MaulikItaliya/Custom-Arduino-Compatible-Board-Design-Altium-/arduino-pcb-design/hardware/Footprint 3d/1825910-6--3DModel-STEP-418109.STEP

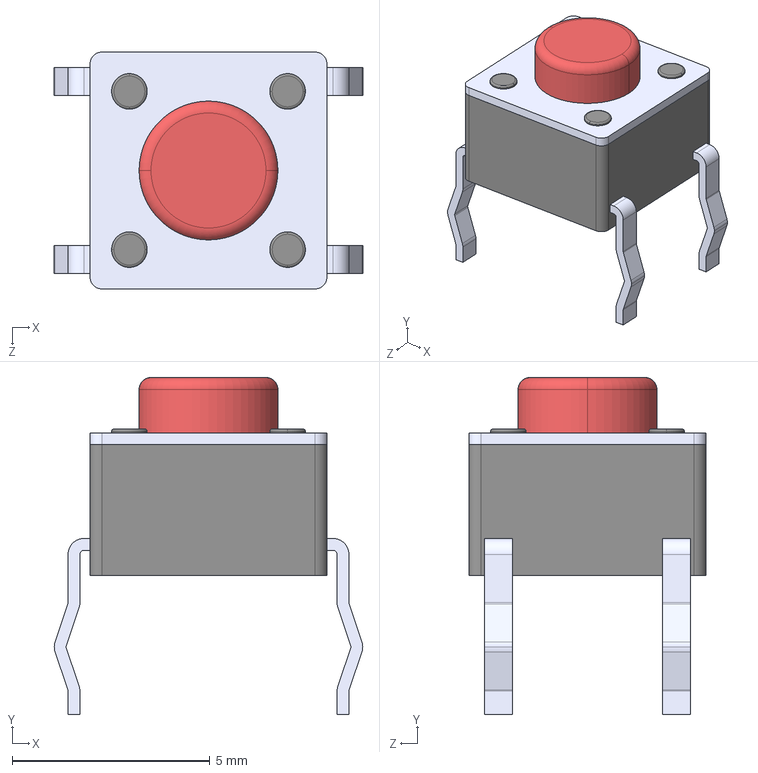
[picture p19: CAD file, 2026-05-17]
arduino-pcb-design/hardware/Footprint 3d/1825910-6--3DModel-STEP-418109.STEP
7.80 x 8.52 x 5.99 mm
