MaulikItaliya/Custom-Arduino-Compatible-Board-Design-Altium-/arduino-pcb-design/hardware/Footprint 3d/m20-7820842.stp

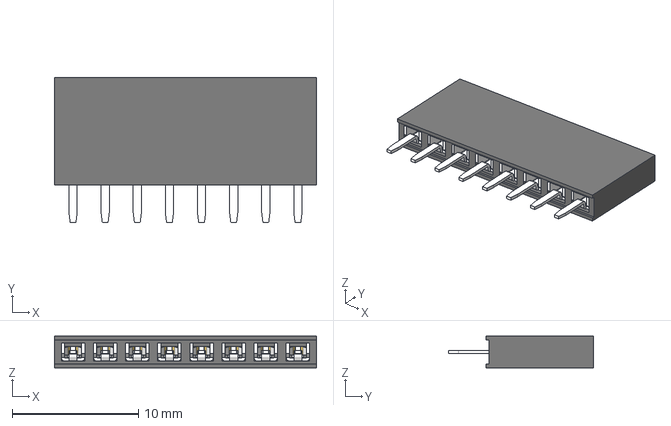
[picture p20: CAD file, 2026-05-17]
arduino-pcb-design/hardware/Footprint 3d/m20-7820842.stp
20.7 x 11.5 x 2.50 mm
