MaulikItaliya/Custom-Arduino-Compatible-Board-Design-Altium-/arduino-pcb-design/hardware/Footprint 3d/68000-103HLF--3DModel-STEP-533217.STEP

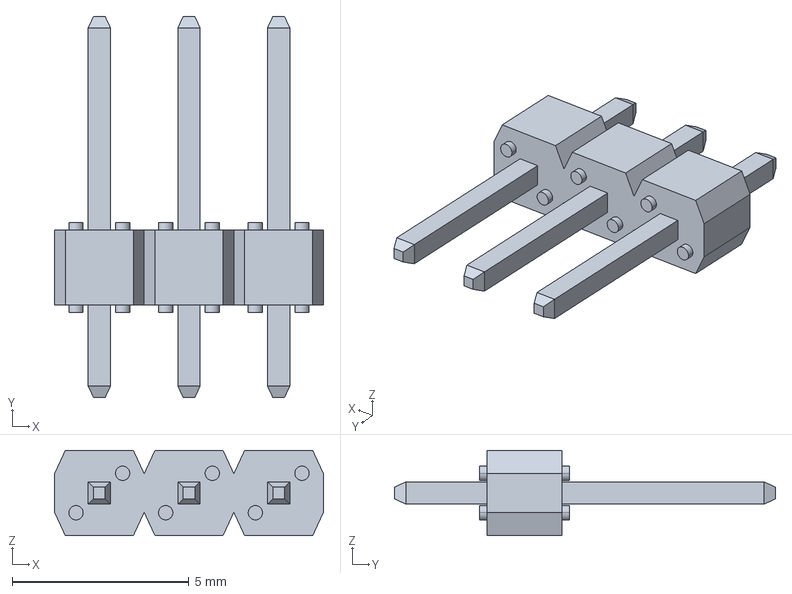
[picture p21: CAD file, 2026-05-17]
arduino-pcb-design/hardware/Footprint 3d/68000-103HLF--3DModel-STEP-533217.STEP
7.62 x 10.8 x 2.41 mm
