MaulikItaliya/Custom-Arduino-Compatible-Board-Design-Altium-/arduino-pcb-design/hardware/Footprint 3d/10118193-0001LF--3DModel-STEP-56544.STEP

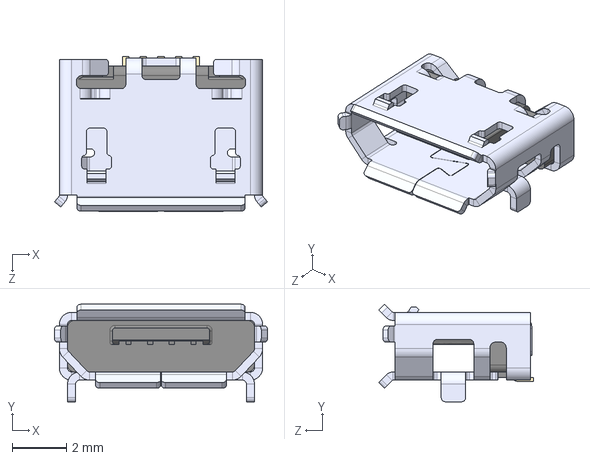
[picture p22: CAD file, 2026-05-17]
arduino-pcb-design/hardware/Footprint 3d/10118193-0001LF--3DModel-STEP-56544.STEP
7.86 x 3.60 x 5.71 mm
